Darexsh/RGB-Ringlight/RGB-Ringlicht_OhneVorwiderstände/photo_2025-12-10_10-47-30 (2).jpg

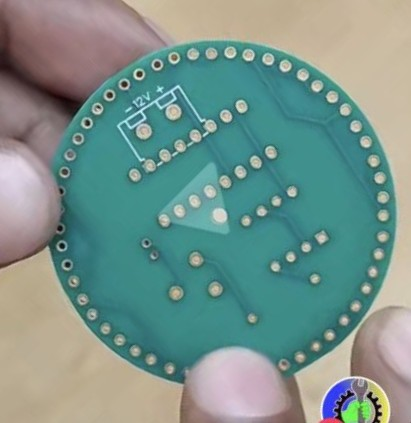
RGB-Ringlicht_OhneVorwiderstände/photo_2025-12-10_10-47-30 (2).jpg
