Darexsh/RGB-Ringlight/RGB-Ringlicht_OhneVorwiderstände/photo_2025-12-10_10-47-30.jpg

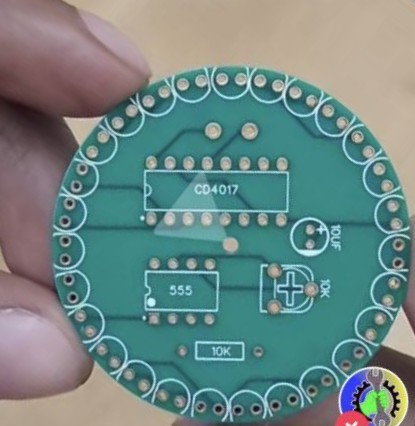
RGB-Ringlicht_OhneVorwiderstände/photo_2025-12-10_10-47-30.jpg
