Darexsh/RGB-Ringlight/RGB-Ringlicht_OhneVorwiderstände/photo_2025-12-11_08-23-33.jpg

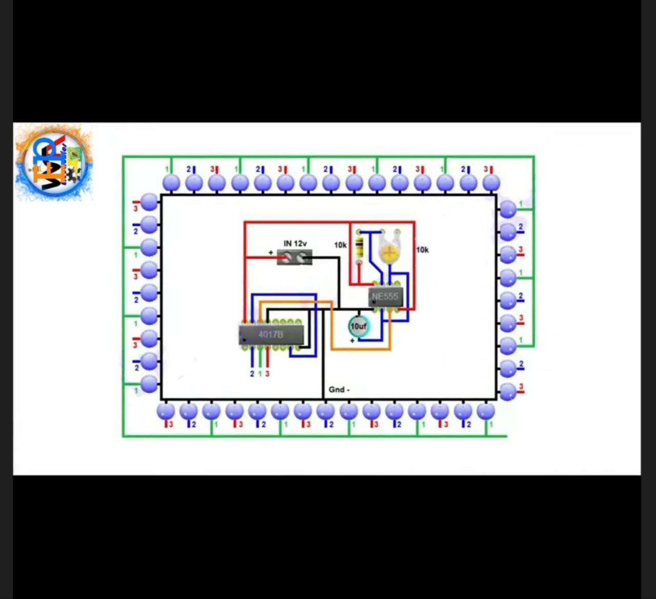
RGB-Ringlicht_OhneVorwiderstände/photo_2025-12-11_08-23-33.jpg
